planedoctor/Countdown_Clock/Supporting Images/20260510_080011.jpg

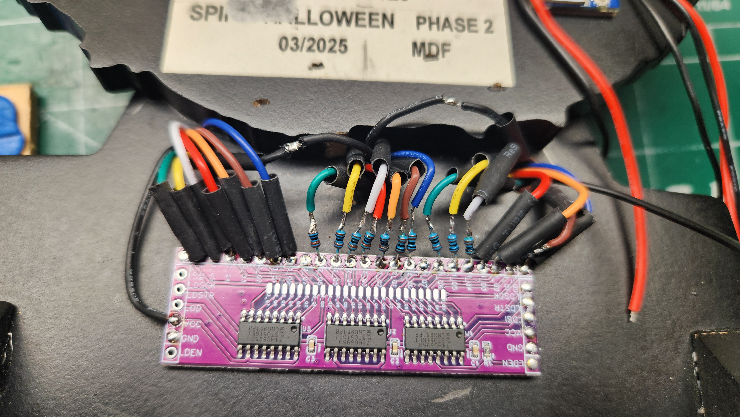
Supporting Images/20260510_080011.jpg
