planedoctor/Countdown_Clock/Supporting Images/20260510_101509.jpg

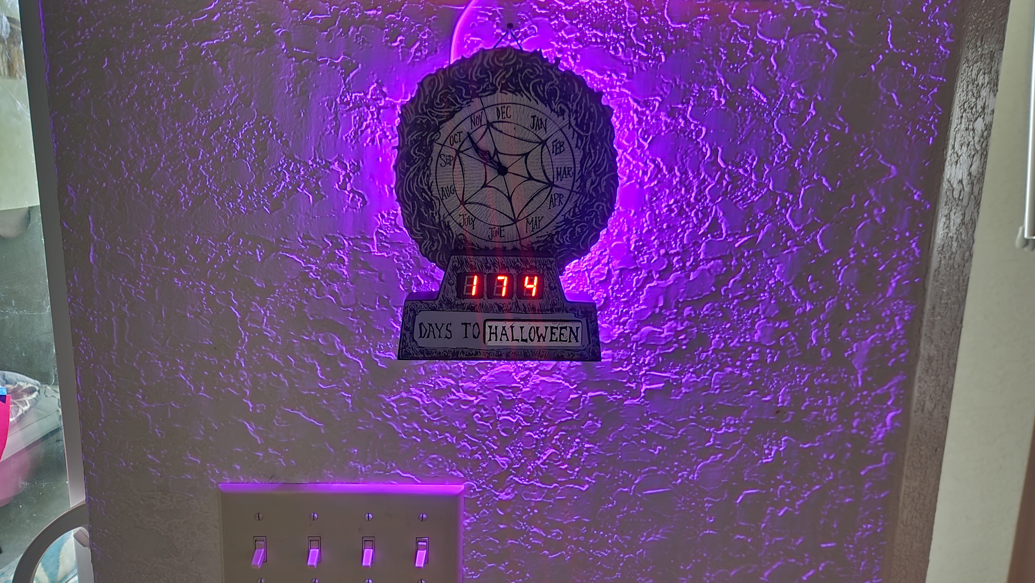
Supporting Images/20260510_101509.jpg
