planedoctor/Countdown_Clock/Supporting Images/20260511_200649.jpg

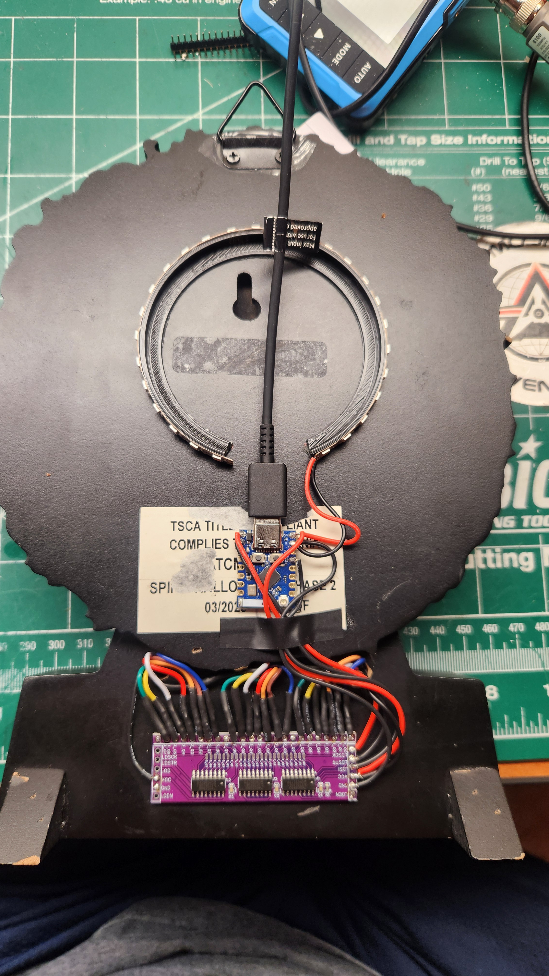
Supporting Images/20260511_200649.jpg
